nicholasshort/MP3-Player/MP3-Player-PCB/3D Models/microsd-socket-slot-like-tfp09-2-12b-tf-01a-etc-1.snapshot.1/002.jpg

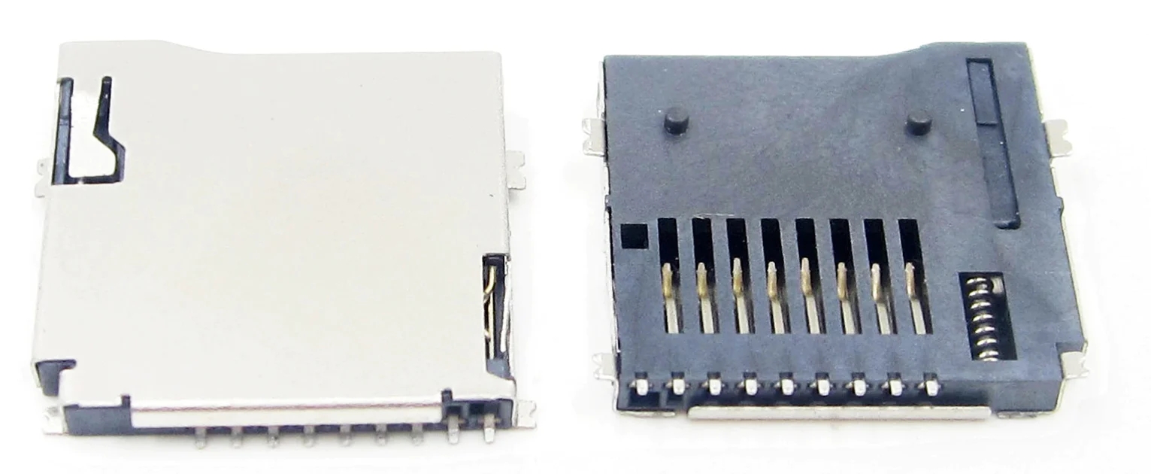
MP3-Player-PCB/3D Models/microsd-socket-slot-like-tfp09-2-12b-tf-01a-etc-1.snapshot.1/002.jpg
